Turaco-System/Turaco-Hardware/PCB/Revision 2/Revision 2.kicad_sch

## KiCad design PCB/Revision 2/Revision 2.kicad_sch (2023-08-22, an earlier design)

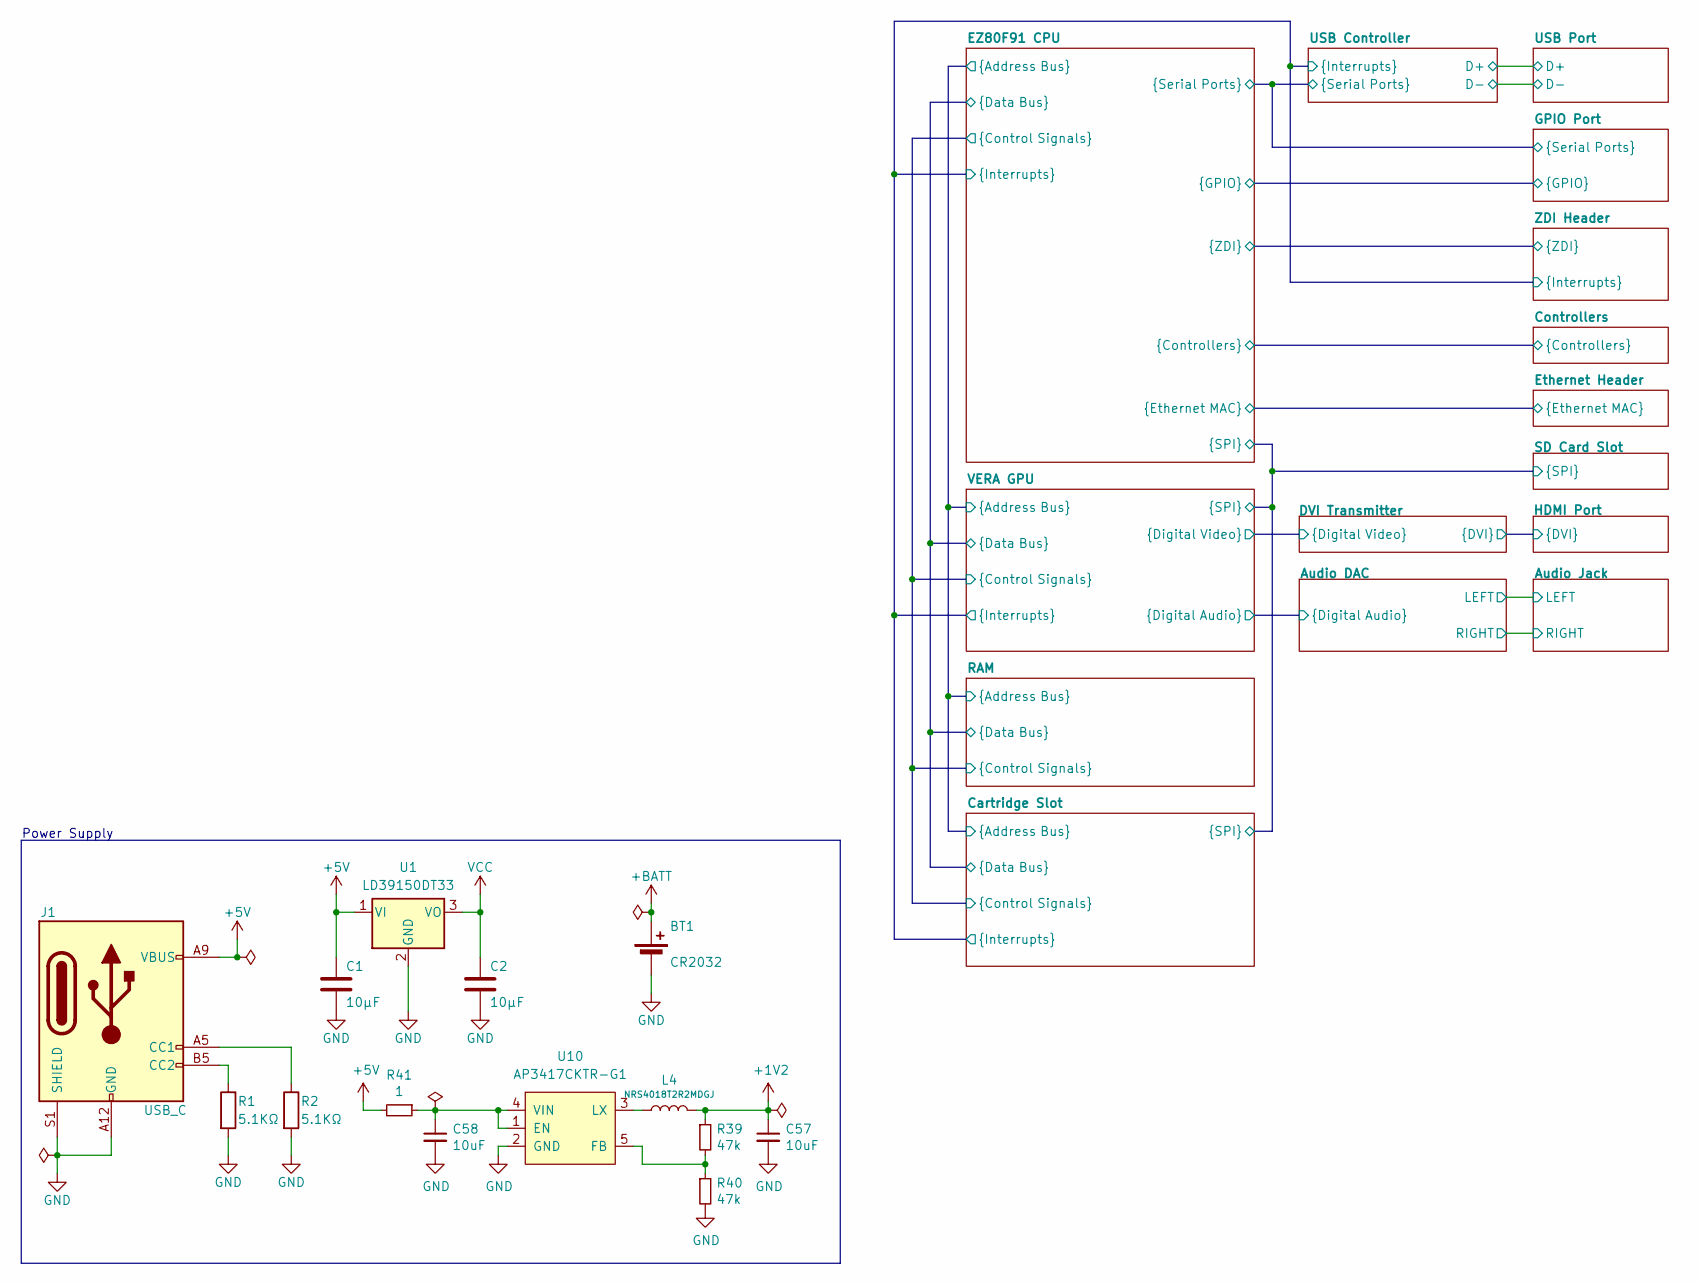
[picture p10: schematic Revision 2.kicad_sch]

Parts:
BT1: CR2032
C1, C2: 10µF
C57, C58: 10uF
J1: USB_C
L4: NRS4018T2R2MDGJ
R1, R2: 5.1KΩ
R39, R40: 47k
R41: 1
U1: LD39150DT33
U10: AP3417CKTR-G1

Connections:
+1V2: C57.1, L4.2, R39.1
+5V: C1.1, J1.A9 (VBUS), J1.B9 (VBUS), R41.2, U1.1 (VI)
+BATT: BT1.1 (+)
GND: BT1.2 (-), C1.2, C2.2, C57.2, C58.2, J1.A12 (GND), J1.B12 (GND), J1.S1 (SHIELD), R1.2, R2.2, R40.2, U1.2 (GND), U10.2 (GND)
unnamed: C58.1, R41.1, U10.1 (EN), U10.4 (VIN)
unnamed: J1.A5 (CC1), R2.1
unnamed: J1.B5 (CC2), R1.1
unnamed: L4.1, U10.3 (LX)
unnamed: R39.2, R40.1, U10.5 (FB)
VCC: C2.1, U1.3 (VO)

Notes on the sheet:
Power Supply
