Turaco-System/Turaco-Hardware/PCB/Revision 2/audio_dac.kicad_sch

## KiCad design PCB/Revision 2/audio_dac.kicad_sch (2023-08-22, an earlier design)

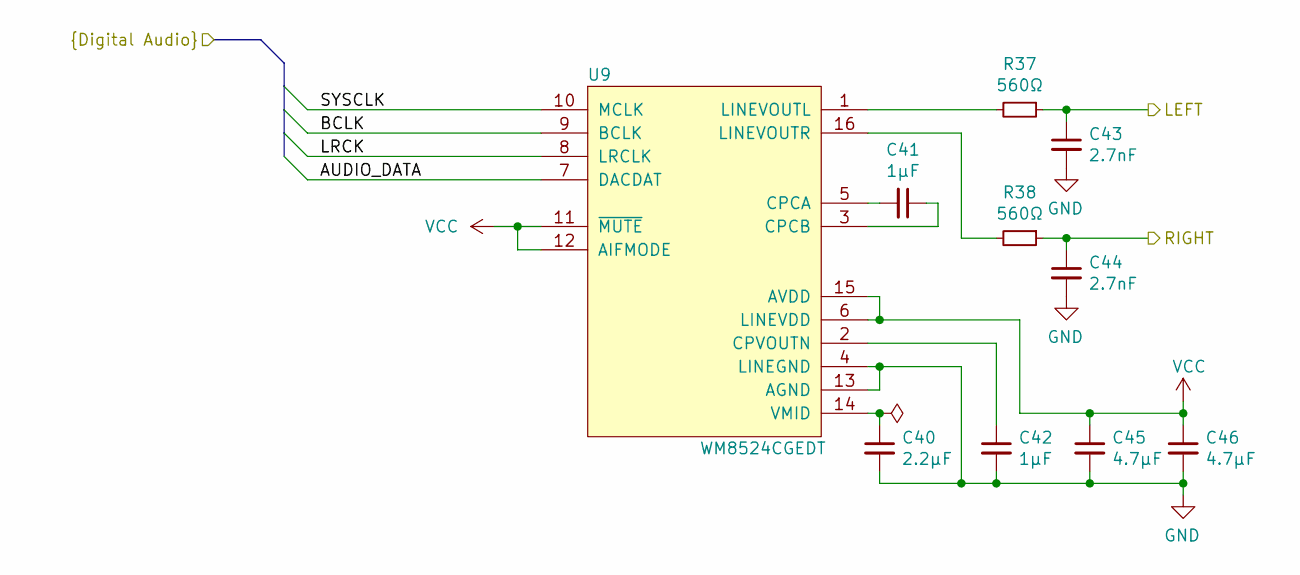
[picture p11: schematic audio_dac.kicad_sch]

Parts:
C40: 2.2µF
C41, C42: 1µF
C43, C44: 2.7nF
C45, C46: 4.7µF
R37, R38: 560Ω
U9: WM8524CGEDT

Connections:
AUDIO_DATA: U9.7 (DACDAT)
BCLK: U9.9 (BCLK)
GND: C40.2, C42.2, C43.2, C44.2, C45.2, C46.2, U9.4 (LINEGND), U9.13 (AGND)
LEFT: C43.1, R37.1
LRCK: U9.8 (LRCLK)
unnamed: C40.1, U9.14 (VMID)
unnamed: C41.1, U9.3 (CPCB)
unnamed: C41.2, U9.5 (CPCA)
unnamed: C42.1, U9.2 (CPVOUTN)
unnamed: R37.2, U9.1 (LINEVOUTL)
unnamed: R38.2, U9.16 (LINEVOUTR)
RIGHT: C44.1, R38.1
SYSCLK: U9.10 (MCLK)
VCC: C45.1, C46.1, U9.6 (LINEVDD), U9.11 (~MUTE), U9.12 (AIFMODE), U9.15 (AVDD)
