Turaco-System/Turaco-Hardware/PCB/Revision 2/controllers.kicad_sch

## KiCad design PCB/Revision 2/controllers.kicad_sch (2023-08-11, an earlier design)

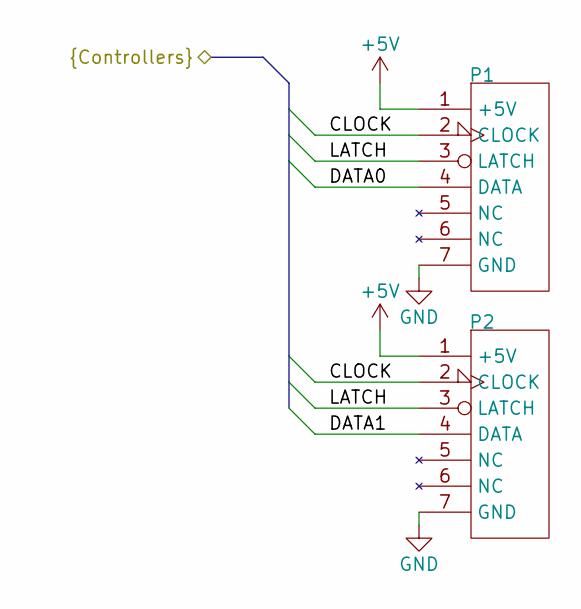
[picture p12: schematic controllers.kicad_sch]

Parts:
P1, P2: (no value)

Connections:
+5V: P1.1 (+5V), P2.1 (+5V)
CLOCK: P1.2 (CLOCK), P2.2 (CLOCK)
DATA0: P1.4 (DATA)
DATA1: P2.4 (DATA)
GND: P1.7 (GND), P2.7 (GND)
LATCH: P1.3 (LATCH), P2.3 (LATCH)
