Turaco-System/Turaco-Hardware/PCB/Revision 2/cpu.kicad_sch

## KiCad design PCB/Revision 2/cpu.kicad_sch (2023-08-22, an earlier design)

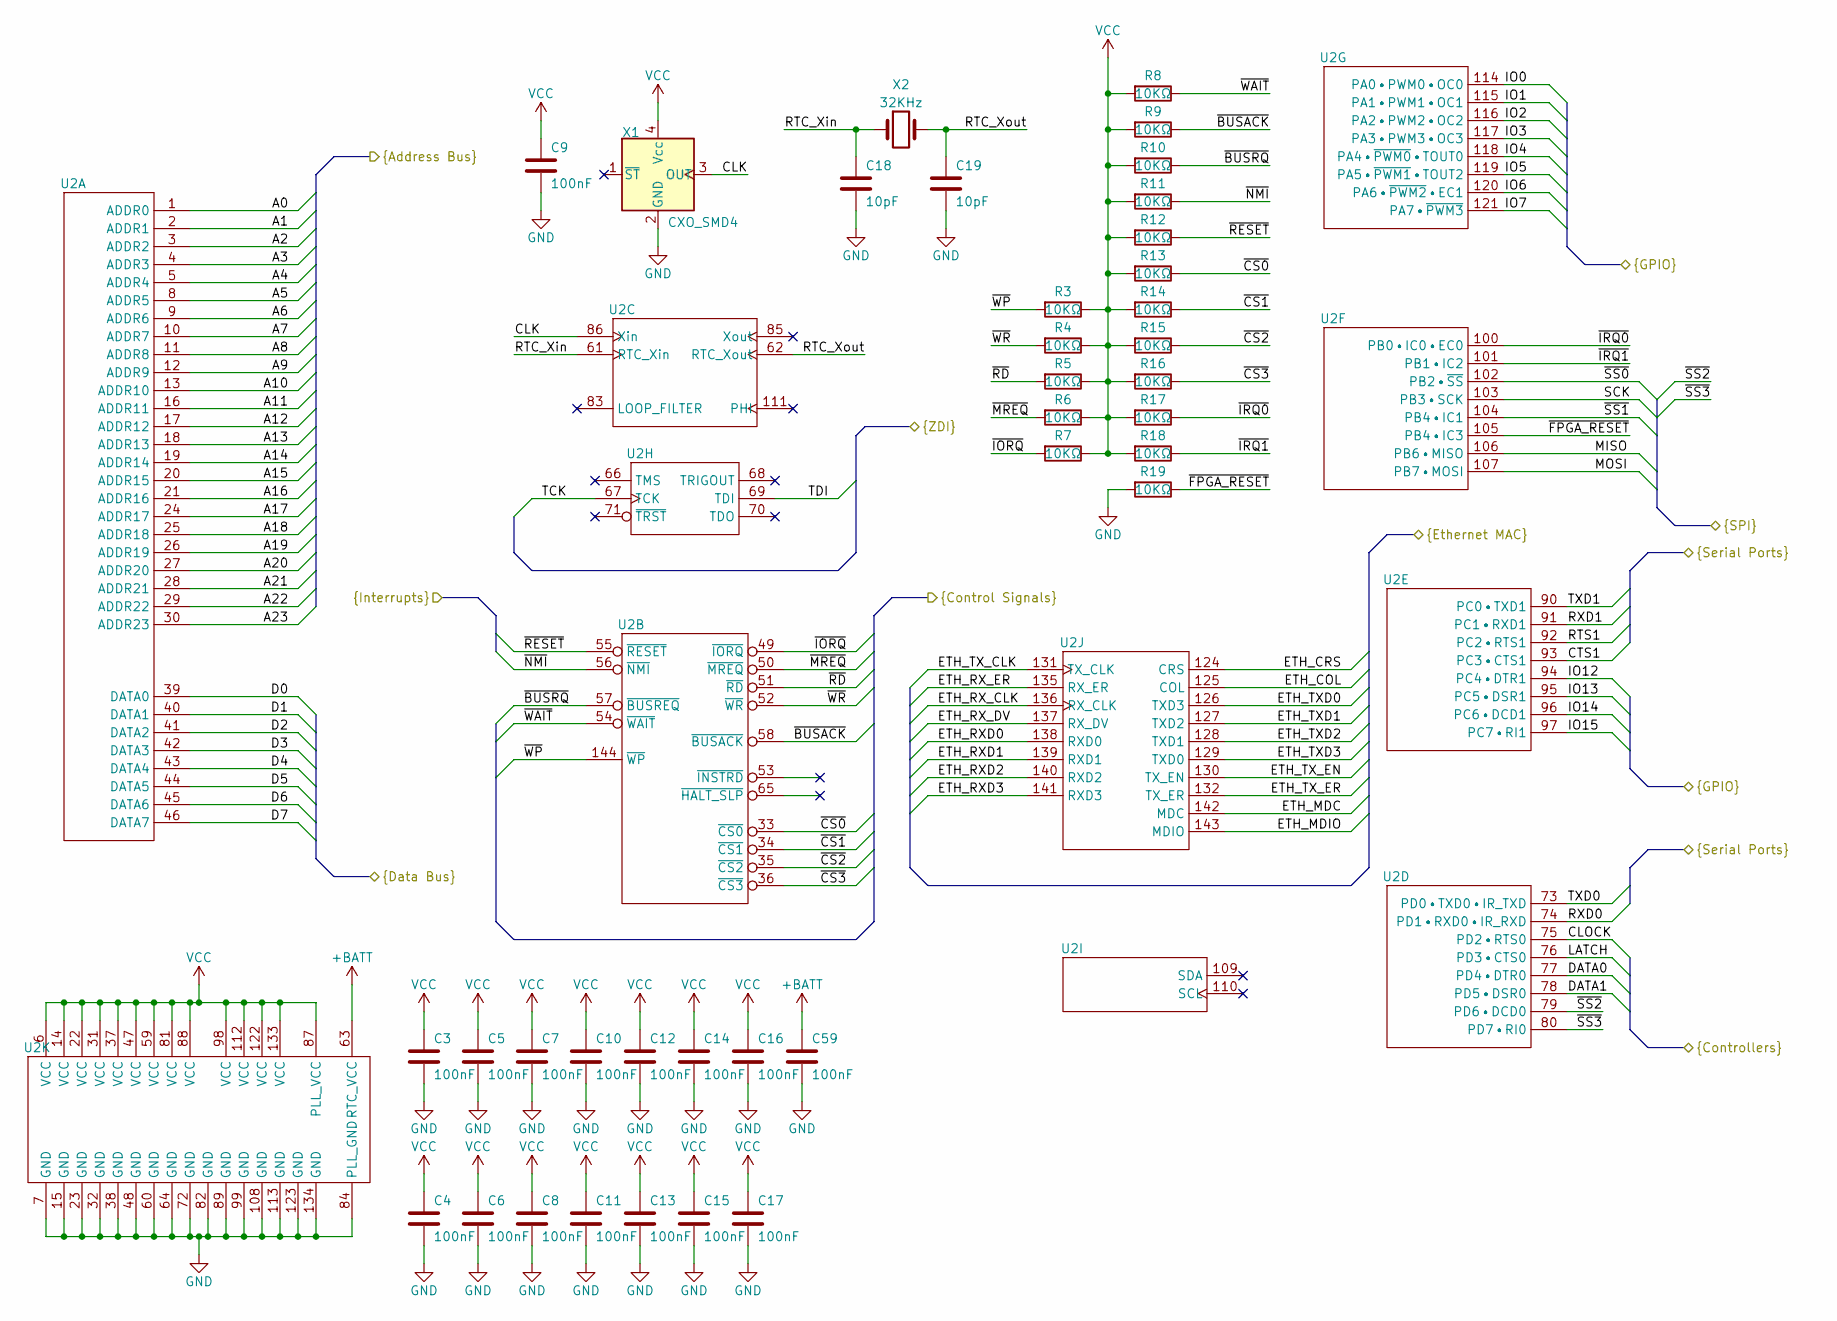
[picture p13: schematic cpu.kicad_sch]

Parts:
C3, C4, C5, C6, C7, C8, C9, C10, C11, C12, C13, C14, C15, C16, C17, C59: 100nF
C18, C19: 10pF
R3, R4, R5, R6, R7, R8, R9, R10, R11, R12, R13, R14, R15, R16, R17, R18, R19: 10KΩ
U2: (no value)
X1: CXO_SMD4
X2: 32KHz

Connections:
+BATT: C59.1, U2.63 (RTC_VCC)
A0: U2.1 (ADDR0)
A1: U2.2 (ADDR1)
A2: U2.3 (ADDR2)
A3: U2.4 (ADDR3)
A4: U2.5 (ADDR4)
A5: U2.8 (ADDR5)
A6: U2.9 (ADDR6)
A7: U2.10 (ADDR7)
A8: U2.11 (ADDR8)
A9: U2.12 (ADDR9)
A10: U2.13 (ADDR10)
A11: U2.16 (ADDR11)
A12: U2.17 (ADDR12)
A13: U2.18 (ADDR13)
A14: U2.19 (ADDR14)
A15: U2.20 (ADDR15)
A16: U2.21 (ADDR16)
A17: U2.24 (ADDR17)
A18: U2.25 (ADDR18)
A19: U2.26 (ADDR19)
A20: U2.27 (ADDR20)
A21: U2.28 (ADDR21)
A22: U2.29 (ADDR22)
A23: U2.30 (ADDR23)
CLK: U2.86 (Xin), X1.3 (OUT)
CLOCK: U2.75 (PD2•RTS0)
CTS1: U2.93 (PC3•CTS1)
D0: U2.39 (DATA0)
D1: U2.40 (DATA1)
D2: U2.41 (DATA2)
D3: U2.42 (DATA3)
D4: U2.43 (DATA4)
D5: U2.44 (DATA5)
D6: U2.45 (DATA6)
D7: U2.46 (DATA7)
DATA0: U2.77 (PD4•DTR0)
DATA1: U2.78 (PD5•DSR0)
ETH_COL: U2.125 (COL)
ETH_CRS: U2.124 (CRS)
ETH_MDC: U2.142 (MDC)
ETH_MDIO: U2.143 (MDIO)
ETH_RXD0: U2.138 (RXD0)
ETH_RXD1: U2.139 (RXD1)
ETH_RXD2: U2.140 (RXD2)
ETH_RXD3: U2.141 (RXD3)
ETH_RX_CLK: U2.136 (RX_CLK)
ETH_RX_DV: U2.137 (RX_DV)
ETH_RX_ER: U2.135 (RX_ER)
ETH_TXD0: U2.126 (TXD3)
ETH_TXD1: U2.127 (TXD2)
ETH_TXD2: U2.128 (TXD1)
ETH_TXD3: U2.129 (TXD0)
ETH_TX_CLK: U2.131 (TX_CLK)
ETH_TX_EN: U2.130 (TX_EN)
ETH_TX_ER: U2.132 (TX_ER)
GND: C3.2, C4.2, C5.2, C6.2, C7.2, C8.2, C9.2, C10.2, C11.2, C12.2, C13.2, C14.2, C15.2, C16.2, C17.2, C18.2, C19.2, C59.2, R19.2, U2.7 (GND), U2.15 (GND), U2.23 (GND), U2.32 (GND), U2.38 (GND), U2.48 (GND), U2.60 (GND), U2.64 (GND), U2.72 (GND), U2.82 (GND), U2.84 (PLL_GND), U2.89 (GND), U2.99 (GND), U2.108 (GND), U2.113 (GND), U2.123 (GND), U2.134 (GND), X1.2 (GND)
IO0: U2.114 (PA0•PWM0•OC0)
IO1: U2.115 (PA1•PWM1•OC1)
IO2: U2.116 (PA2•PWM2•OC2)
IO3: U2.117 (PA3•PWM3•OC3)
IO4: U2.118 (PA4•~PWM0•TOUT0)
IO5: U2.119 (PA5•~PWM1•TOUT2)
IO6: U2.120 (PA6•~PWM2•EC1)
IO7: U2.121 (PA7•~PWM3)
IO12: U2.94 (PC4•DTR1)
IO13: U2.95 (PC5•DSR1)
IO14: U2.96 (PC6•DCD1)
IO15: U2.97 (PC7•RI1)
LATCH: U2.76 (PD3•CTS0)
MISO: U2.106 (PB6•MISO)
MOSI: U2.107 (PB7•MOSI)
RTC_Xin: C18.1, U2.61 (RTC_Xin), X2.1
RTC_Xout: C19.1, U2.62 (RTC_Xout), X2.2
RTS1: U2.92 (PC2•RTS1)
RXD0: U2.74 (PD1•RXD0•IR_RXD)
RXD1: U2.91 (PC1•RXD1)
SCK: U2.103 (PB3•SCK)
TCK: U2.67 (TCK)
TDI: U2.69 (TDI)
TXD0: U2.73 (PD0•TXD0•IR_TXD)
TXD1: U2.90 (PC0•TXD1)
VCC: C3.1, C4.1, C5.1, C6.1, C7.1, C8.1, C9.1, C10.1, C11.1, C12.1, C13.1, C14.1, C15.1, C16.1, C17.1, R3.1, R4.1, R5.1, R6.1, R7.1, R8.2, R9.2, R10.2, R11.2, R12.2, R13.2, R14.2, R15.2, R16.2, R17.2, R18.2, U2.6 (VCC), U2.14 (VCC), U2.22 (VCC), U2.31 (VCC), U2.37 (VCC), U2.47 (VCC), U2.59 (VCC), U2.81 (VCC), U2.87 (PLL_VCC), U2.88 (VCC), U2.98 (VCC), U2.112 (VCC), U2.122 (VCC), U2.133 (VCC), X1.4 (Vcc)
~BUSACK: R9.1, U2.58 (~BUSACK)
~BUSRQ: R10.1, U2.57 (~BUSREQ)
~CS0: R13.1, U2.33 (~CS0)
~CS1: R14.1, U2.34 (~CS1)
~CS2: R15.1, U2.35 (~CS2)
~CS3: R16.1, U2.36 (~CS3)
~FPGA_RESET: R19.1, U2.105 (PB4•IC3)
~IORQ: R7.2, U2.49 (~IORQ)
~IRQ0: R17.1, U2.100 (PB0•IC0•EC0)
~IRQ1: R18.1, U2.101 (PB1•IC2)
~MREQ: R6.2, U2.50 (~MREQ)
~NMI: R11.1, U2.56 (~NMI)
~RD: R5.2, U2.51 (~RD)
~RESET: R12.1, U2.55 (~RESET)
~SS0: U2.102 (PB2•~SS)
~SS1: U2.104 (PB4•IC1)
~SS2: U2.79 (PD6•DCD0)
~SS3: U2.80 (PD7•RI0)
~WAIT: R8.1, U2.54 (~WAIT)
~WP: R3.2, U2.144 (~WP)
~WR: R4.2, U2.52 (~WR)
