Turaco-System/Turaco-Hardware/PCB/Revision 2/dvi_transmitter.kicad_sch

## KiCad design PCB/Revision 2/dvi_transmitter.kicad_sch (2023-08-22, an earlier design)

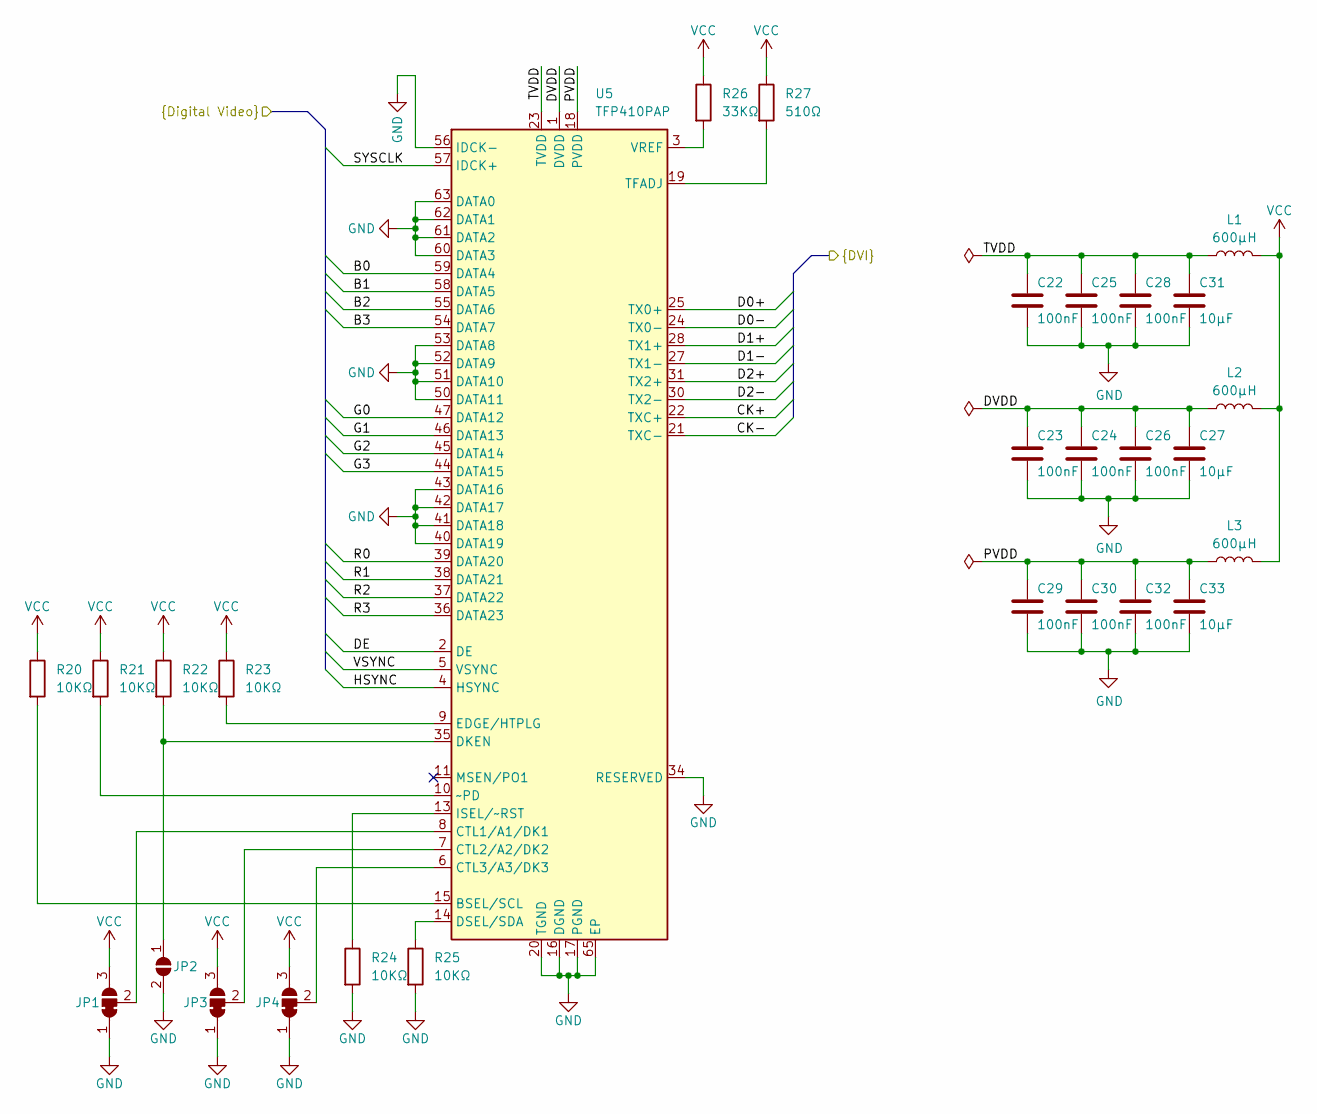
[picture p14: schematic dvi_transmitter.kicad_sch]

Parts:
C22, C23, C24, C25, C26, C28, C29, C30, C32: 100nF
C27, C31, C33: 10µF
JP1, JP3, JP4: SolderJumper_3_Bridged12
JP2: SolderJumper_2_Open
L1, L2, L3: 600µH
R20, R21, R22, R23, R24, R25: 10KΩ
R26: 33KΩ
R27: 510Ω
U5: TFP410PAP

Connections:
B0: U5.59 (DATA4)
B1: U5.58 (DATA5)
B2: U5.55 (DATA6)
B3: U5.54 (DATA7)
CK+: U5.22 (TXC+)
CK-: U5.21 (TXC-)
D0+: U5.25 (TX0+)
D0-: U5.24 (TX0-)
D1+: U5.28 (TX1+)
D1-: U5.27 (TX1-)
D2+: U5.31 (TX2+)
D2-: U5.30 (TX2-)
DE: U5.2 (DE)
DVDD: C23.1, C24.1, C26.1, C27.1, L2.1, U5.1 (DVDD), U5.12 (DVDD), U5.33 (DVDD)
G0: U5.47 (DATA12)
G1: U5.46 (DATA13)
G2: U5.45 (DATA14)
G3: U5.44 (DATA15)
GND: C22.2, C23.2, C24.2, C25.2, C26.2, C27.2, C28.2, C29.2, C30.2, C31.2, C32.2, C33.2, JP1.1 (A), JP2.2 (B), JP3.1 (A), JP4.1 (A), R24.2, R25.2, U5.16 (DGND), U5.17 (PGND), U5.20 (TGND), U5.26 (TGND), U5.32 (TGND), U5.34 (RESERVED), U5.40 (DATA19), U5.41 (DATA18), U5.42 (DATA17), U5.43 (DATA16), U5.48 (DGND), U5.50 (DATA11), U5.51 (DATA10), U5.52 (DATA9), U5.53 (DATA8), U5.56 (IDCK-), U5.60 (DATA3), U5.61 (DATA2), U5.62 (DATA1), U5.63 (DATA0), U5.64 (DGND), U5.65 (EP)
HSYNC: U5.4 (HSYNC)
unnamed: JP1.2 (C), U5.8 (CTL1/A1/DK1)
unnamed: JP2.1 (A), R22.2, U5.35 (DKEN)
unnamed: JP3.2 (C), U5.7 (CTL2/A2/DK2)
unnamed: JP4.2 (C), U5.6 (CTL3/A3/DK3)
unnamed: R20.2, U5.15 (BSEL/SCL)
unnamed: R21.2, U5.10 (~PD)
unnamed: R23.2, U5.9 (EDGE/HTPLG)
unnamed: R24.1, U5.13 (ISEL/~RST)
unnamed: R25.1, U5.14 (DSEL/SDA)
unnamed: R26.2, U5.3 (VREF)
unnamed: R27.2, U5.19 (TFADJ)
PVDD: C29.1, C30.1, C32.1, C33.1, L3.1, U5.18 (PVDD)
R0: U5.39 (DATA20)
R1: U5.38 (DATA21)
R2: U5.37 (DATA22)
R3: U5.36 (DATA23)
SYSCLK: U5.57 (IDCK+)
TVDD: C22.1, C25.1, C28.1, C31.1, L1.1, U5.23 (TVDD), U5.29 (TVDD)
VCC: JP1.3 (B), JP3.3 (B), JP4.3 (B), L1.2, L2.2, L3.2, R20.1, R21.1, R22.1, R23.1, R26.1, R27.1
VSYNC: U5.5 (VSYNC)
