Turaco-System/Turaco-Hardware/PCB/Revision 2/power_supply.kicad_sch

## KiCad design PCB/Revision 2/power_supply.kicad_sch (2023-08-10)

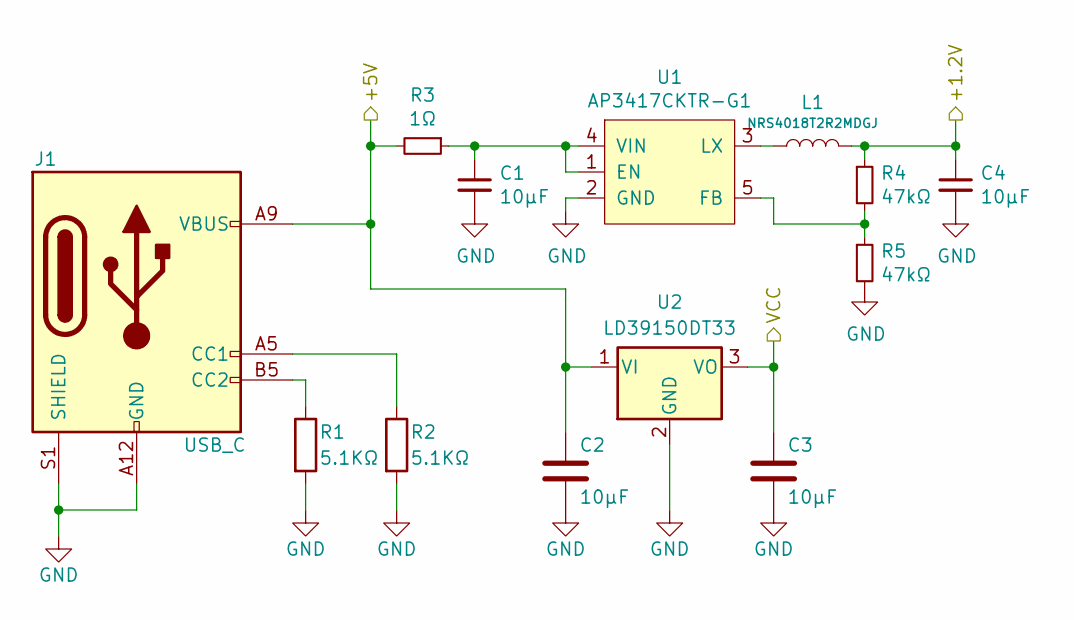
[picture p15: schematic power_supply.kicad_sch]

Parts:
C1, C4: 10µF; C_0805_2012Metric
C2, C3: 10µF
J1: USB_C
L1: NRS4018T2R2MDGJ; L_Bourns-SRN4018
R1, R2: 5.1KΩ
R3: 1Ω; R_0603_1608Metric
R4, R5: 47kΩ; R_0603_1608Metric
U1: AP3417CKTR-G1; SOT-23-5
U2: LD39150DT33; TO-252-3_TabPin2

Connections:
+1.2V: C4.1, L1.2, R4.1
+5V: C2.1, J1.A9 (VBUS), J1.B9 (VBUS), R3.2, U2.1 (VI)
GND: C1.2, C2.2, C3.2, C4.2, J1.A12 (GND), J1.B12 (GND), J1.S1 (SHIELD), R1.2, R2.2, R5.2, U1.2 (GND), U2.2 (GND)
unnamed: C1.1, R3.1, U1.1 (EN), U1.4 (VIN)
unnamed: J1.A5 (CC1), R2.1
unnamed: J1.B5 (CC2), R1.1
unnamed: L1.1, U1.3 (LX)
unnamed: R4.2, R5.1, U1.5 (FB)
VCC: C3.1, U2.3 (VO)
