Turaco-System/Turaco-Hardware/PCB/Revision 2/ram.kicad_sch

## KiCad design PCB/Revision 2/ram.kicad_sch (2023-08-22, an earlier design)

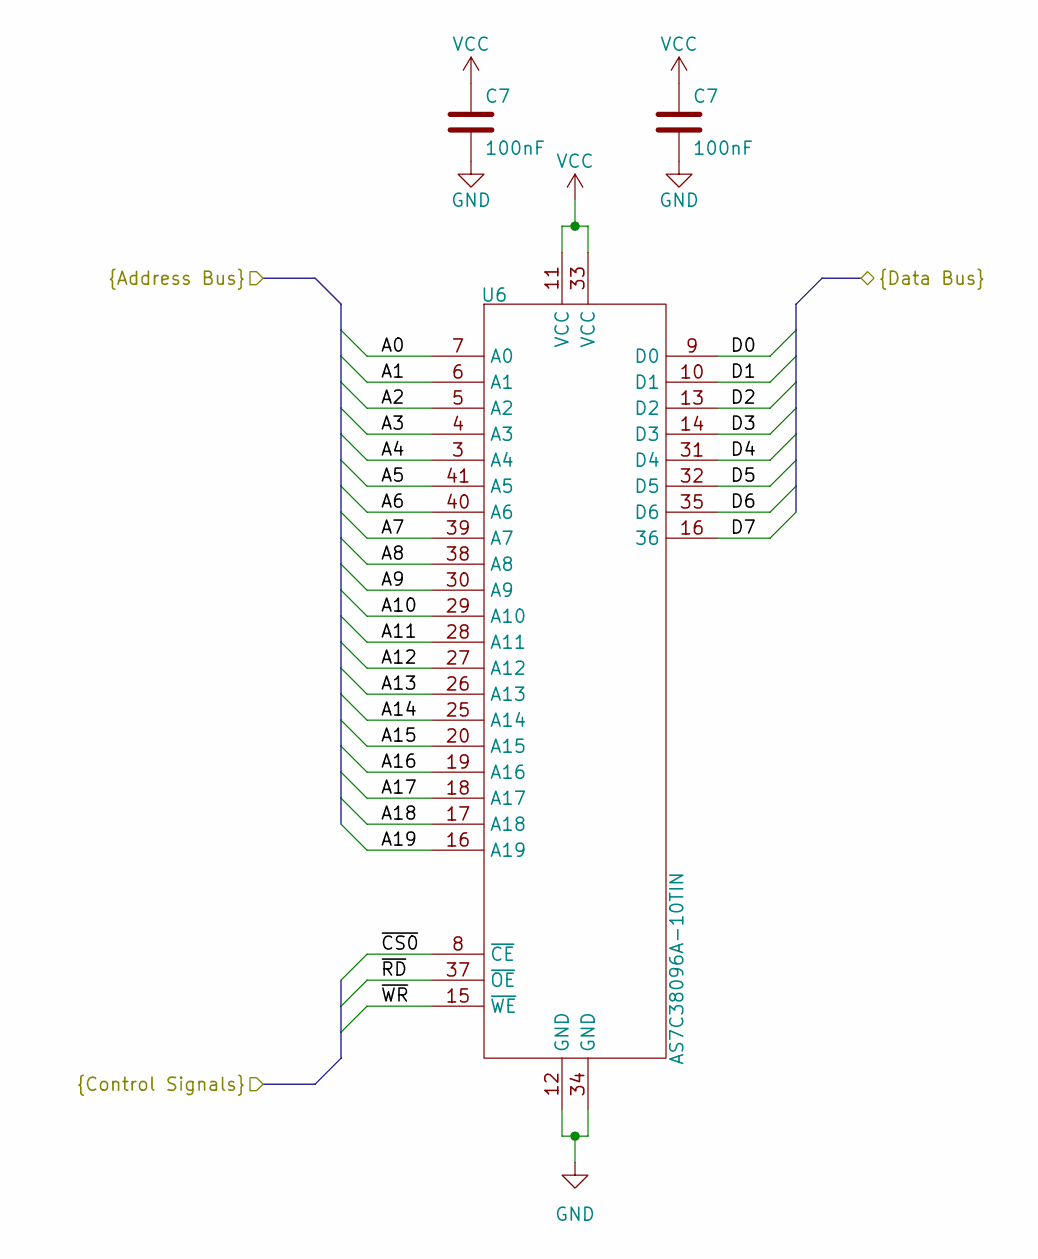
[picture p16: schematic ram.kicad_sch]

Parts:
C7: 100nF
U6: AS7C38096A-10TIN

Connections:
A0: U6.7 (A0)
A1: U6.6 (A1)
A2: U6.5 (A2)
A3: U6.4 (A3)
A4: U6.3 (A4)
A5: U6.41 (A5)
A6: U6.40 (A6)
A7: U6.39 (A7)
A8: U6.38 (A8)
A9: U6.30 (A9)
A10: U6.29 (A10)
A11: U6.28 (A11)
A12: U6.27 (A12)
A13: U6.26 (A13)
A14: U6.25 (A14)
A15: U6.20 (A15)
A16: U6.19 (A16)
A17: U6.18 (A17)
A18: U6.17 (A18)
A19: U6.16 (36)
D0: U6.9 (D0)
D1: U6.10 (D1)
D2: U6.13 (D2)
D3: U6.14 (D3)
D4: U6.31 (D4)
D5: U6.32 (D5)
D6: U6.35 (D6)
D7: U6.16 (36)
GND: C7.2, U6.12 (GND), U6.34 (GND)
VCC: C7.1, U6.11 (VCC), U6.33 (VCC)
~CS0: U6.8 (~CE)
~RD: U6.37 (~OE)
~WR: U6.15 (~WE)
