Turaco-System/Turaco-Hardware/PCB/Revision 2/sd_card.kicad_sch

## KiCad design PCB/Revision 2/sd_card.kicad_sch (2023-08-22, an earlier design)

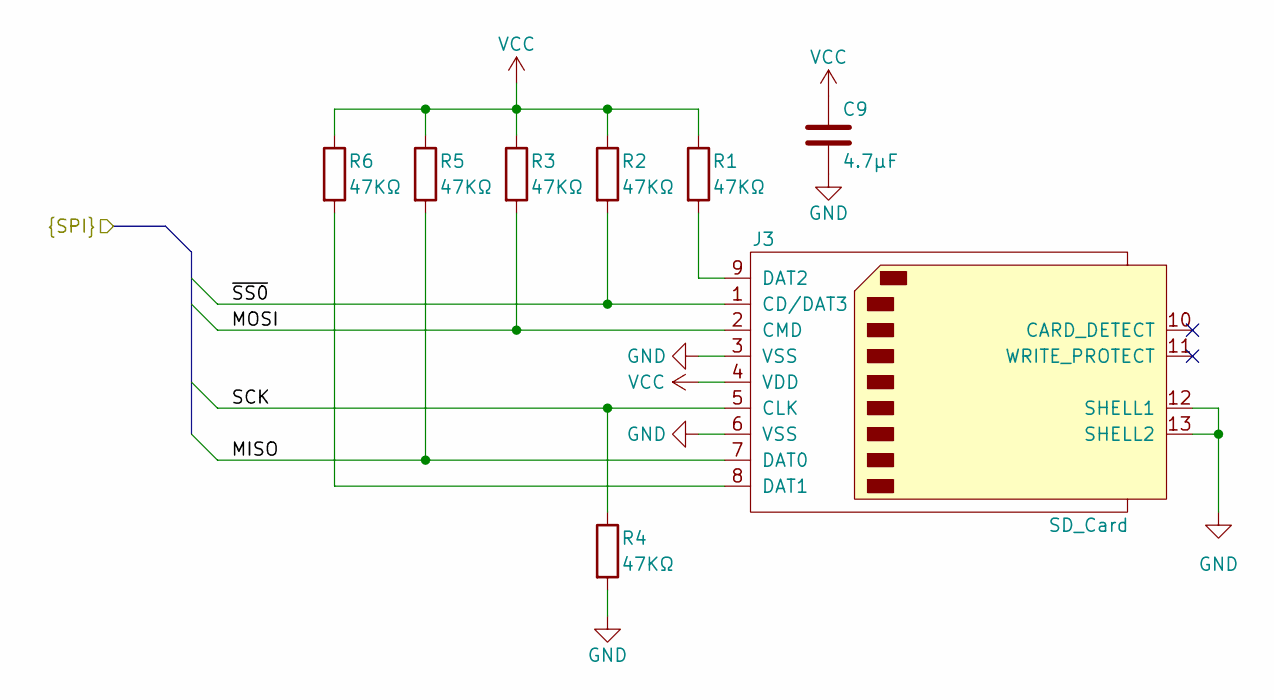
[picture p17: schematic sd_card.kicad_sch]

Parts:
C9: 4.7µF
J3: SD_Card
R1, R2, R3, R4, R5, R6: 47KΩ

Connections:
GND: C9.2, J3.3 (VSS), J3.6 (VSS), J3.12 (SHELL1), J3.13 (SHELL2), R4.2
MISO: J3.7 (DAT0), R5.2
MOSI: J3.2 (CMD), R3.2
unnamed: J3.8 (DAT1), R6.2
unnamed: J3.9 (DAT2), R1.2
SCK: J3.5 (CLK), R4.1
VCC: C9.1, J3.4 (VDD), R1.1, R2.1, R3.1, R5.1, R6.1
~SS0: J3.1 (CD/DAT3), R2.2
