Turaco-System/Turaco-Hardware/PCB/Revision 2/usb_controller.kicad_sch

## KiCad design PCB/Revision 2/usb_controller.kicad_sch (2023-08-22, an earlier design)

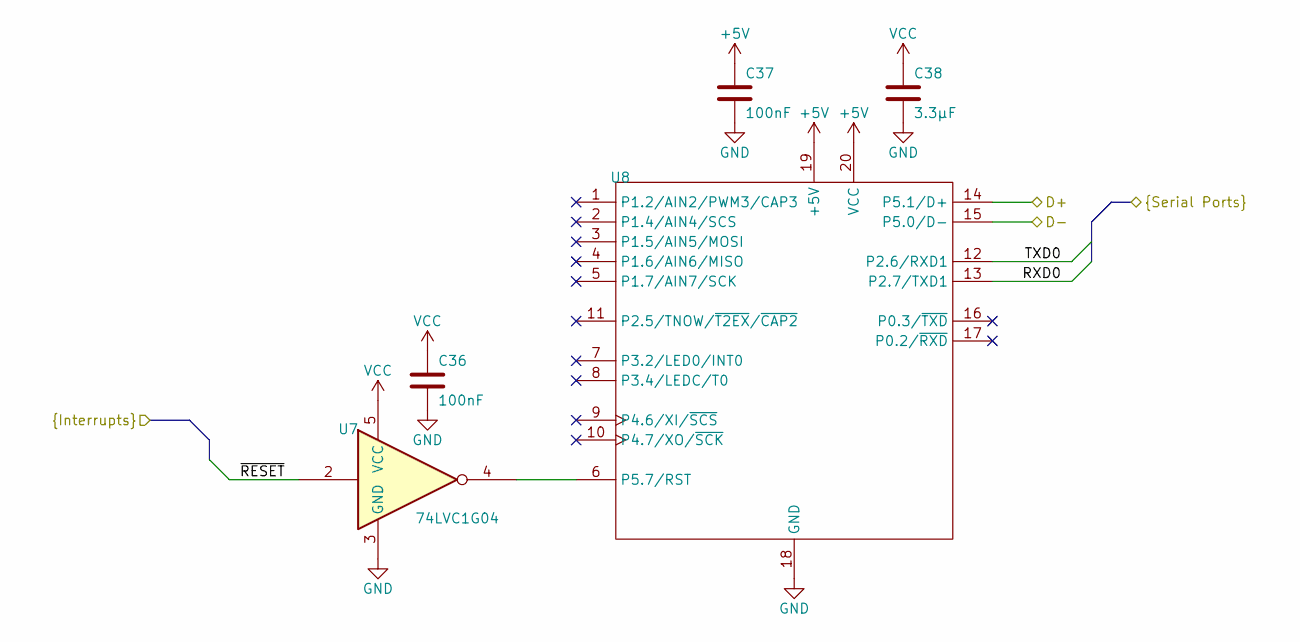
[picture p18: schematic usb_controller.kicad_sch]

Parts:
C36, C37: 100nF
C38: 3.3µF
U7: 74LVC1G04
U8: (no value)

Connections:
+5V: C37.1, U8.19 (+5V), U8.20 (VCC)
D+: U8.14 (P5.1/D+)
D-: U8.15 (P5.0/D-)
GND: C36.2, C37.2, C38.2, U7.3 (GND), U8.18 (GND)
unnamed: U7.4, U8.6 (P5.7/RST)
RXD0: U8.13 (P2.7/TXD1)
TXD0: U8.12 (P2.6/RXD1)
VCC: C36.1, C38.1, U7.5 (VCC)
~RESET: U7.2
