Turaco-System/Turaco-Hardware/PCB/Revision 2/vera.kicad_sch

## KiCad design PCB/Revision 2/vera.kicad_sch (2023-08-22, an earlier design)

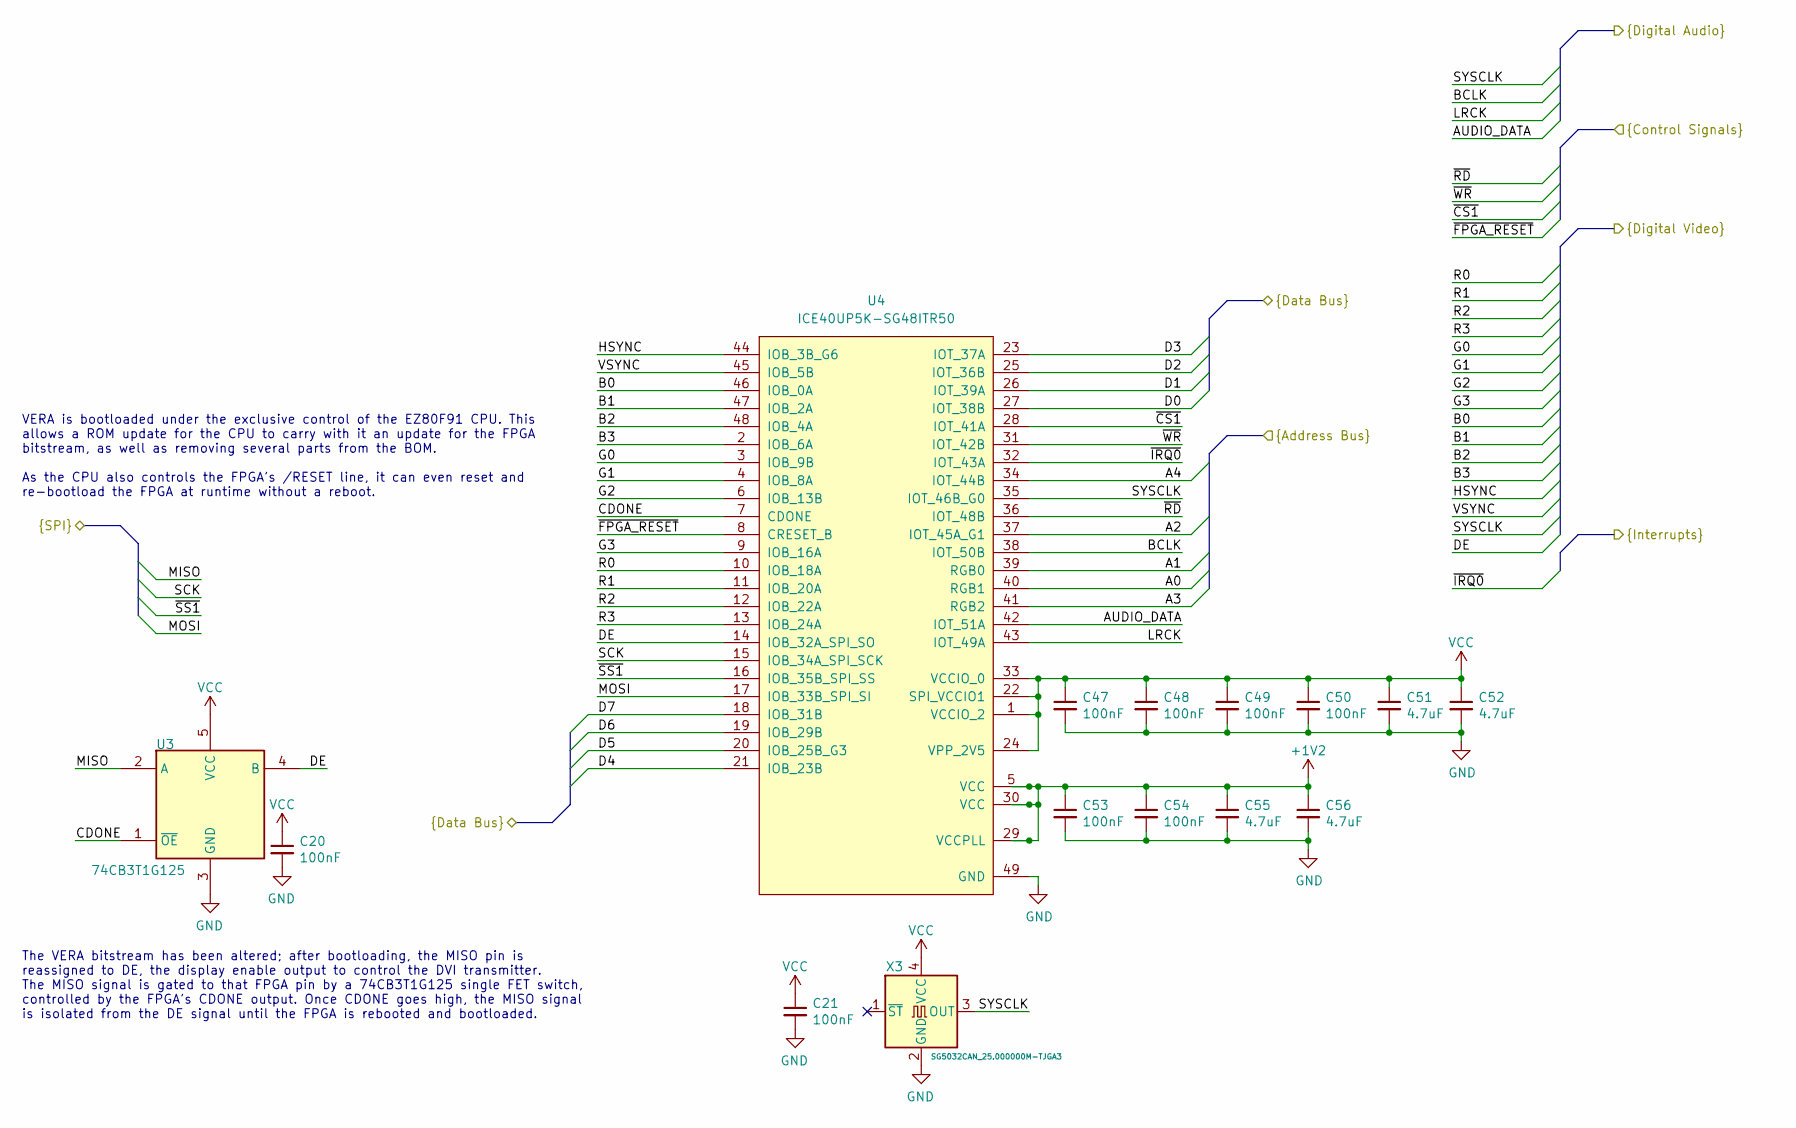
[picture p19: schematic vera.kicad_sch]

Parts:
C20, C21, C47, C48, C49, C50, C53, C54: 100nF
C51, C52, C55, C56: 4.7uF
U3: 74CB3T1G125
U4: ICE40UP5K-SG48ITR50
X3: SG5032CAN_25.000000M-TJGA3

Connections:
+1V2: C53.1, C54.1, C55.1, C56.1, U4.5 (VCC), U4.29 (VCCPLL), U4.30 (VCC)
A0: U4.40 (RGB1)
A1: U4.39 (RGB0)
A2: U4.37 (IOT_45A_G1)
A3: U4.41 (RGB2)
A4: U4.34 (IOT_44B)
AUDIO_DATA: U4.42 (IOT_51A)
B0: U4.46 (IOB_0A)
B1: U4.47 (IOB_2A)
B2: U4.48 (IOB_4A)
B3: U4.2 (IOB_6A)
BCLK: U4.38 (IOT_50B)
CDONE: U3.1 (~OE), U4.7 (CDONE)
D0: U4.27 (IOT_38B)
D1: U4.26 (IOT_39A)
D2: U4.25 (IOT_36B)
D3: U4.23 (IOT_37A)
D4: U4.21 (IOB_23B)
D5: U4.20 (IOB_25B_G3)
D6: U4.19 (IOB_29B)
D7: U4.18 (IOB_31B)
DE: U3.4 (B), U4.14 (IOB_32A_SPI_SO)
G0: U4.3 (IOB_9B)
G1: U4.4 (IOB_8A)
G2: U4.6 (IOB_13B)
G3: U4.9 (IOB_16A)
GND: C20.2, C21.2, C47.2, C48.2, C49.2, C50.2, C51.2, C52.2, C53.2, C54.2, C55.2, C56.2, U3.3 (GND), U4.49 (GND), X3.2 (GND)
HSYNC: U4.44 (IOB_3B_G6)
LRCK: U4.43 (IOT_49A)
MISO: U3.2 (A)
MOSI: U4.17 (IOB_33B_SPI_SI)
R0: U4.10 (IOB_18A)
R1: U4.11 (IOB_20A)
R2: U4.12 (IOB_22A)
R3: U4.13 (IOB_24A)
SCK: U4.15 (IOB_34A_SPI_SCK)
SYSCLK: U4.35 (IOT_46B_G0), X3.3 (OUT)
VCC: C20.1, C21.1, C47.1, C48.1, C49.1, C50.1, C51.1, C52.1, U3.5 (VCC), U4.1 (VCCIO_2), U4.22 (SPI_VCCIO1), U4.24 (VPP_2V5), U4.33 (VCCIO_0), X3.4 (VCC)
VSYNC: U4.45 (IOB_5B)
~CS1: U4.28 (IOT_41A)
~FPGA_RESET: U4.8 (CRESET_B)
~IRQ0: U4.32 (IOT_43A)
~RD: U4.36 (IOT_48B)
~SS1: U4.16 (IOB_35B_SPI_SS)
~WR: U4.31 (IOT_42B)

Notes on the sheet:
VERA is bootloaded under the exclusive control of the EZ80F91 CPU. This allows a ROM update for the CPU to carry with it an update for the FPGA bitstream, as well as removing several parts from the BOM. As the CPU also controls the FPGA's /RESET line, it can even reset and re-bootload the FPGA at r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
The VERA bitstream has been altered; after bootloading, the MISO pin is reassigned to DE, the display enable output to control the DVI transmitter. The MISO signal is gated to that FPGA pin by a 74CB3T1G125 single FET switch, controlled by the FPGA's CDONE output. Once CDONE goes high, the MISO sig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
