Turaco-System/Turaco-Hardware/PCB/Revision 2/video_dac.kicad_sch

## KiCad design PCB/Revision 2/video_dac.kicad_sch (2023-08-10)

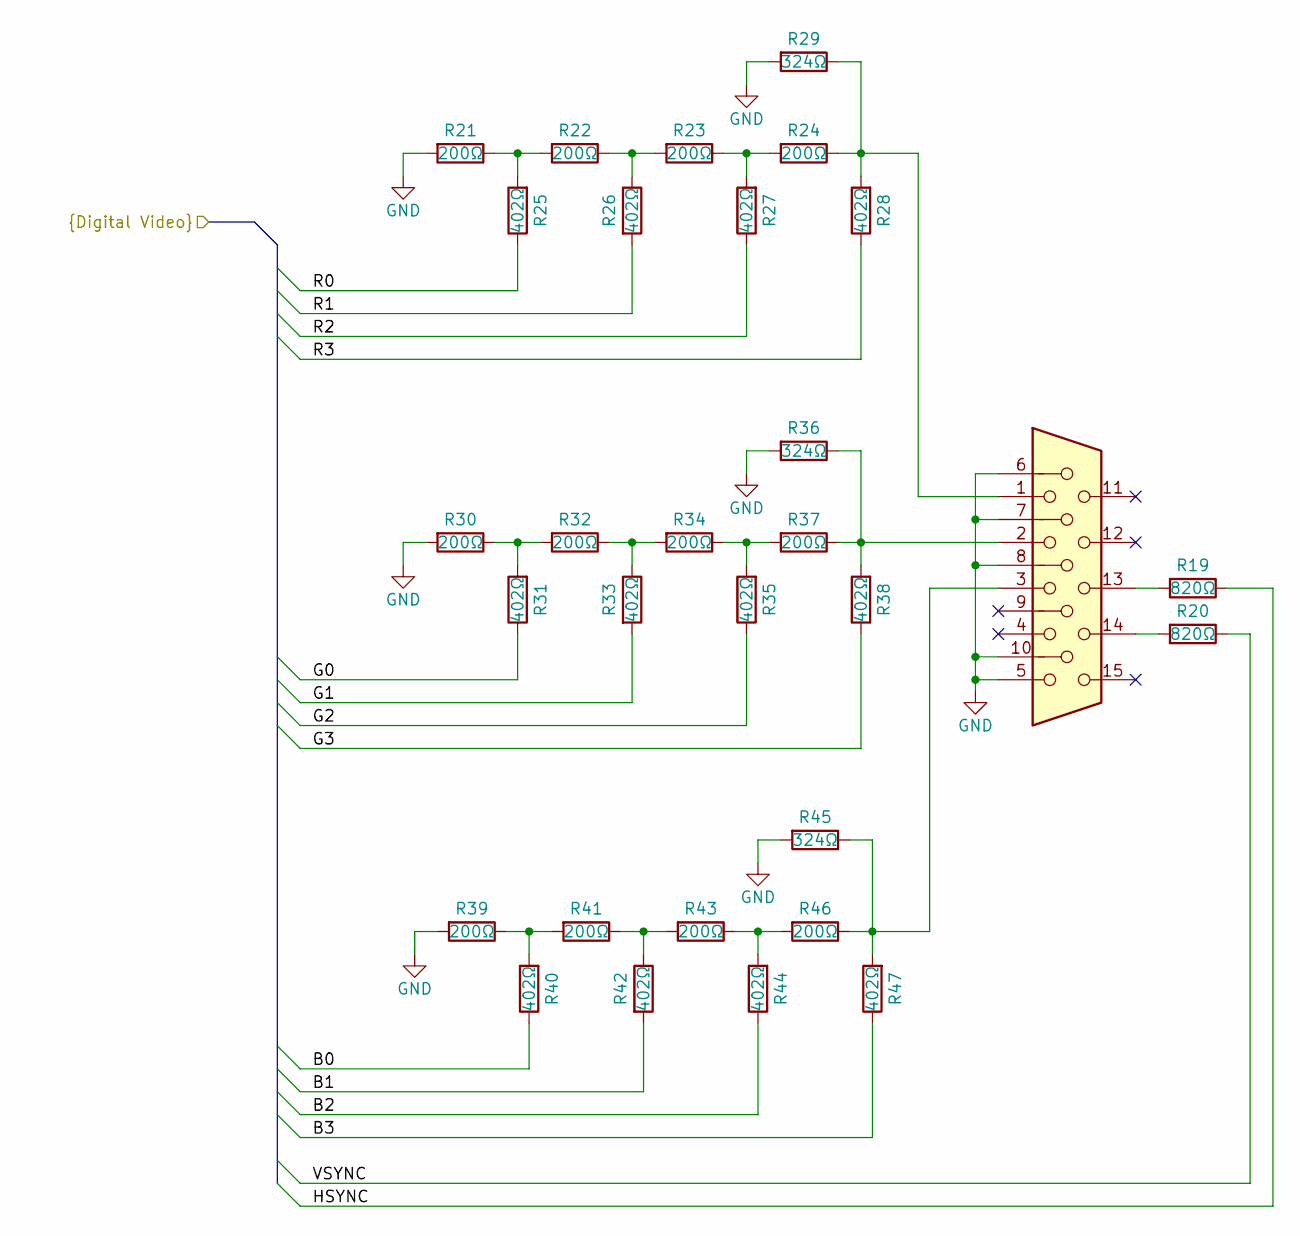
[picture p20: schematic video_dac.kicad_sch]

Parts:
J1: DE15_Receptacle_HighDensity
R19, R20: 820Ω
R21, R22, R23, R24, R30, R32, R34, R37, R39, R41, R43, R46: 200Ω
R25, R26, R27, R28, R31, R33, R35, R38, R40, R42, R44, R47: 402Ω
R29, R36, R45: 324Ω

Connections:
B0: R40.1
B1: R42.2
B2: R44.1
B3: R47.1
G0: R31.1
G1: R33.2
G2: R35.1
G3: R38.1
GND: J1.5, J1.6, J1.7, J1.8, J1.10, R21.2, R29.2, R30.2, R36.2, R39.2, R45.2
HSYNC: R19.1
unnamed: J1.1, R24.1, R28.2, R29.1
unnamed: J1.2, R36.1, R37.1, R38.2
unnamed: J1.3, R45.1, R46.1, R47.2
unnamed: J1.13, R19.2
unnamed: J1.14, R20.2
unnamed: R21.1, R22.2, R25.2
unnamed: R22.1, R23.2, R26.1
unnamed: R23.1, R24.2, R27.2
unnamed: R30.1, R31.2, R32.2
unnamed: R32.1, R33.1, R34.2
unnamed: R34.1, R35.2, R37.2
unnamed: R39.1, R40.2, R41.2
unnamed: R41.1, R42.1, R43.2
unnamed: R43.1, R44.2, R46.2
R0: R25.1
R1: R26.2
R2: R27.1
R3: R28.1
VSYNC: R20.1
