Turaco-System/Turaco-Hardware/PCB/Revision 2/zdi_header.kicad_sch

## KiCad design PCB/Revision 2/zdi_header.kicad_sch (2023-08-22, an earlier design)

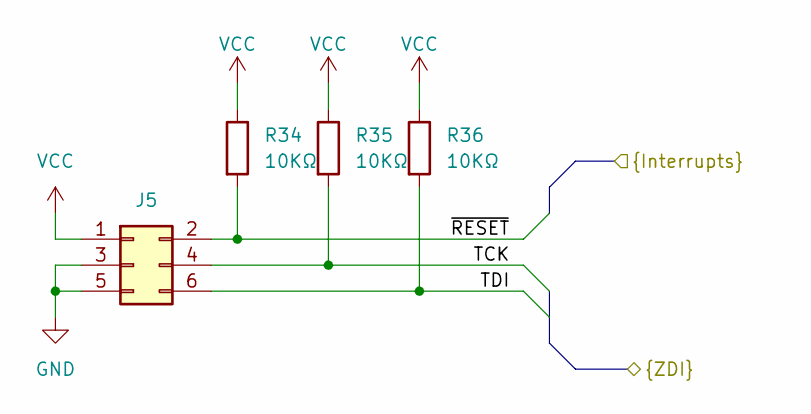
[picture p21: schematic zdi_header.kicad_sch]

Parts:
J5: Conn_02x03_Odd_Even
R34, R35, R36: 10KΩ

Connections:
GND: J5.3, J5.5
TCK: J5.4, R35.2
TDI: J5.6, R36.2
VCC: J5.1, R34.1, R35.1, R36.1
~RESET: J5.2, R34.2
